IronPineOutdoors/IPC101/mechanical/enclosure/branding/reference_crosswind_concept/crosswind_detail.png

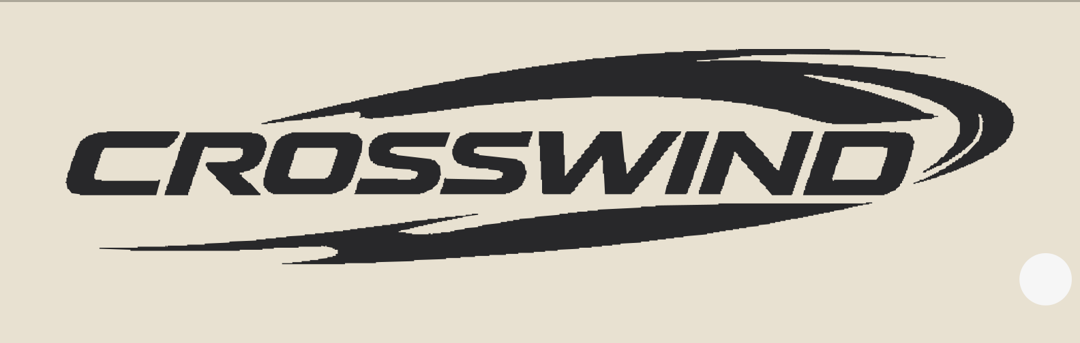
mechanical/enclosure/branding/reference_crosswind_concept/crosswind_detail.png
