IronPineOutdoors/IPC101/mechanical/enclosure/branding/reference_crosswind_concept/faceplate.png

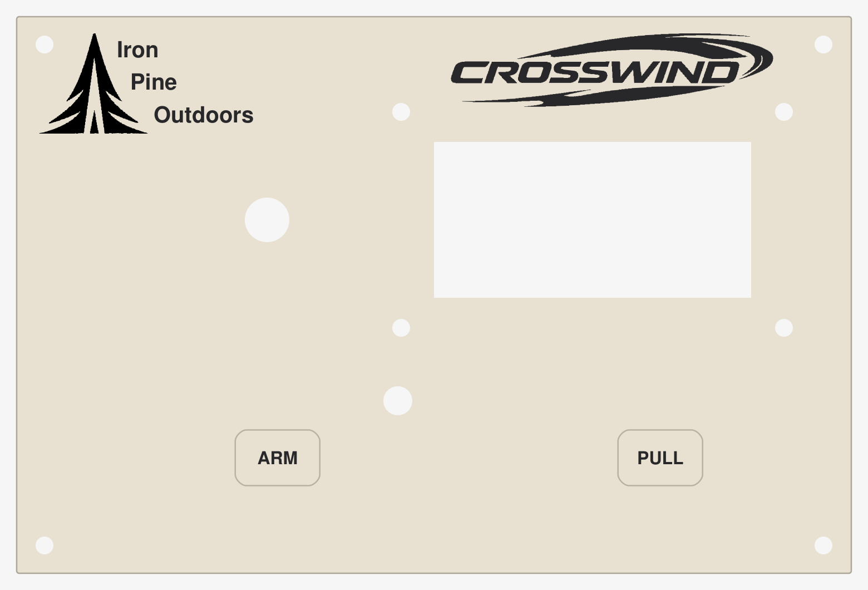
mechanical/enclosure/branding/reference_crosswind_concept/faceplate.png
