IronPineOutdoors/IPC101/mechanical/enclosure/controls/buttons/R1_button_caps_preview.png

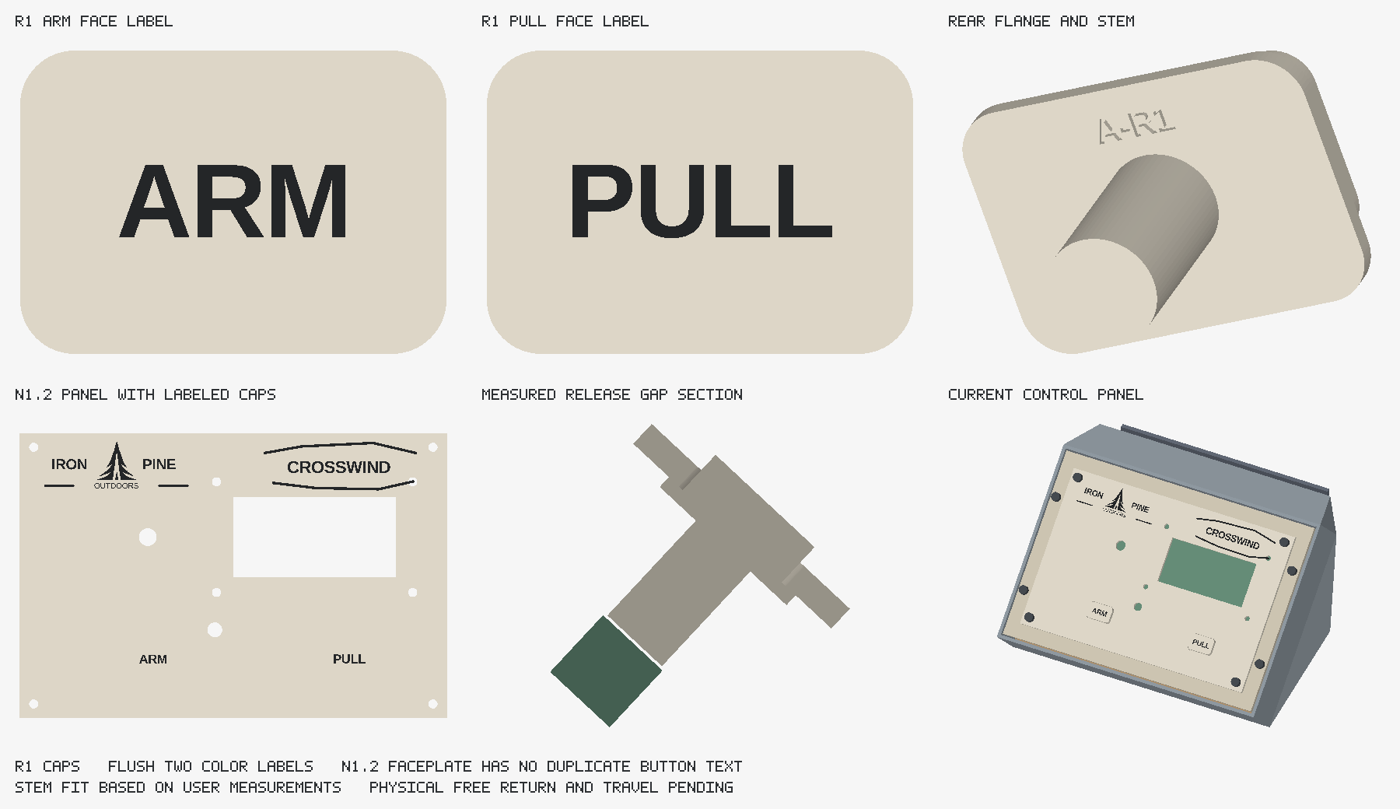
mechanical/enclosure/controls/buttons/R1_button_caps_preview.png
