IronPineOutdoors/IPC101/mechanical/enclosure/controls/led/LED_R1_preview.png

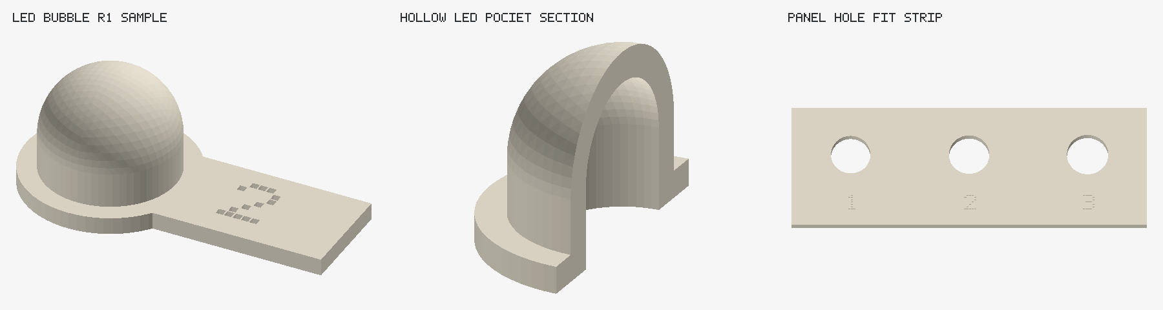
mechanical/enclosure/controls/led/LED_R1_preview.png
