IronPineOutdoors/IPC101/mechanical/enclosure/controls/stop/side-pod/STOP_S1_preview.png

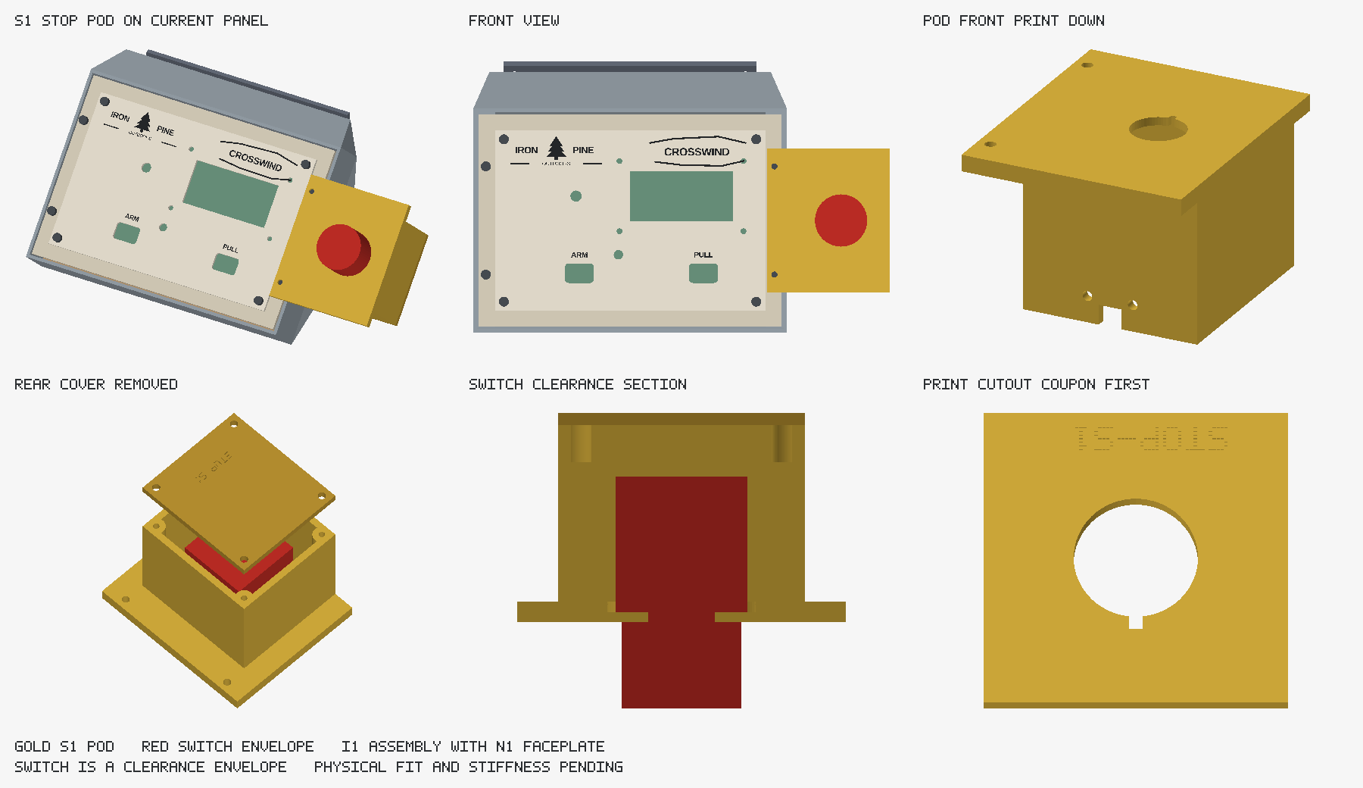
mechanical/enclosure/controls/stop/side-pod/STOP_S1_preview.png
