IronPineOutdoors/IPC101/mechanical/enclosure/controls/stop/top-mounted/TOP_STOP_R3_preview.png

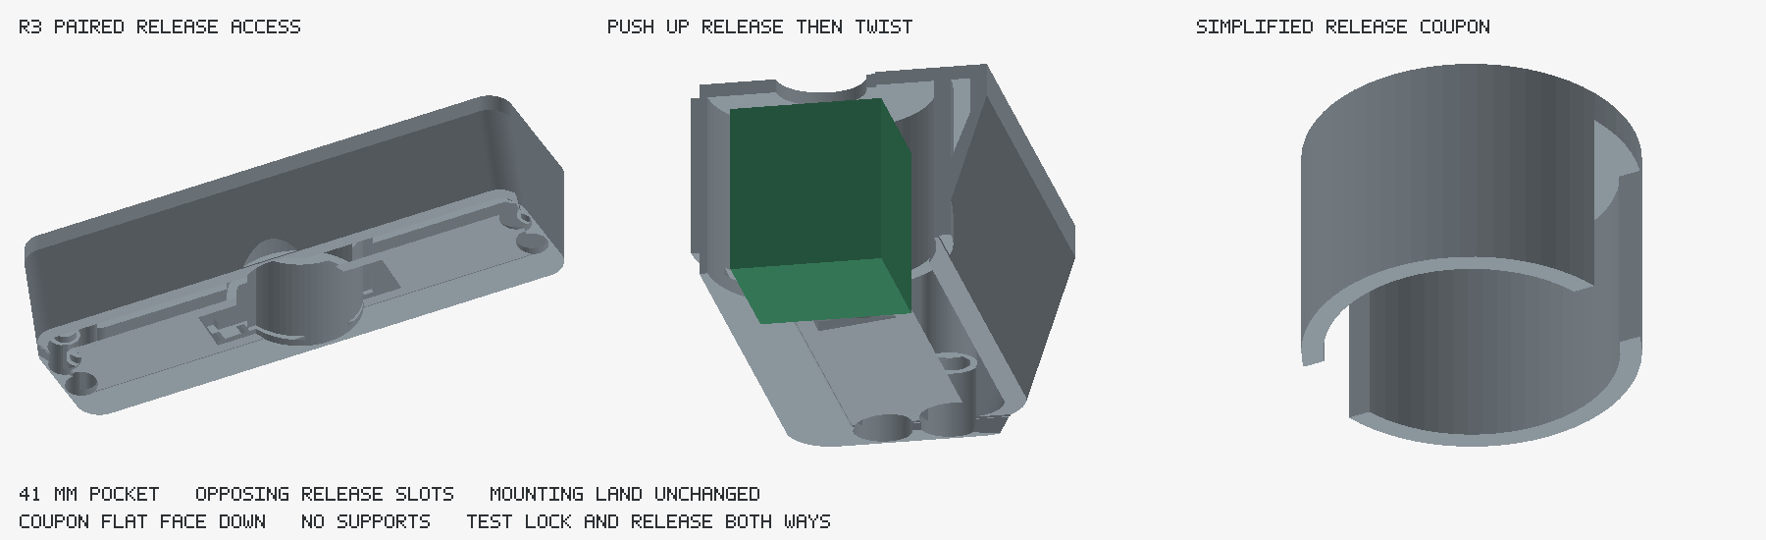
mechanical/enclosure/controls/stop/top-mounted/TOP_STOP_R3_preview.png
