IronPineOutdoors/IPC101/mechanical/enclosure/mounting/RevH_preview.png

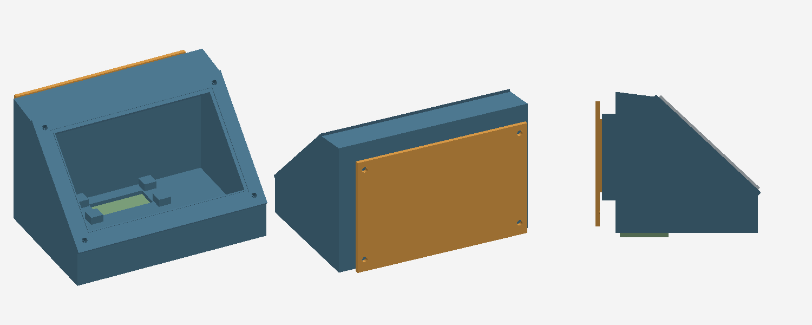
mechanical/enclosure/mounting/RevH_preview.png
