IronPineOutdoors/IPC101/mechanical/enclosure/RevI_preview.png

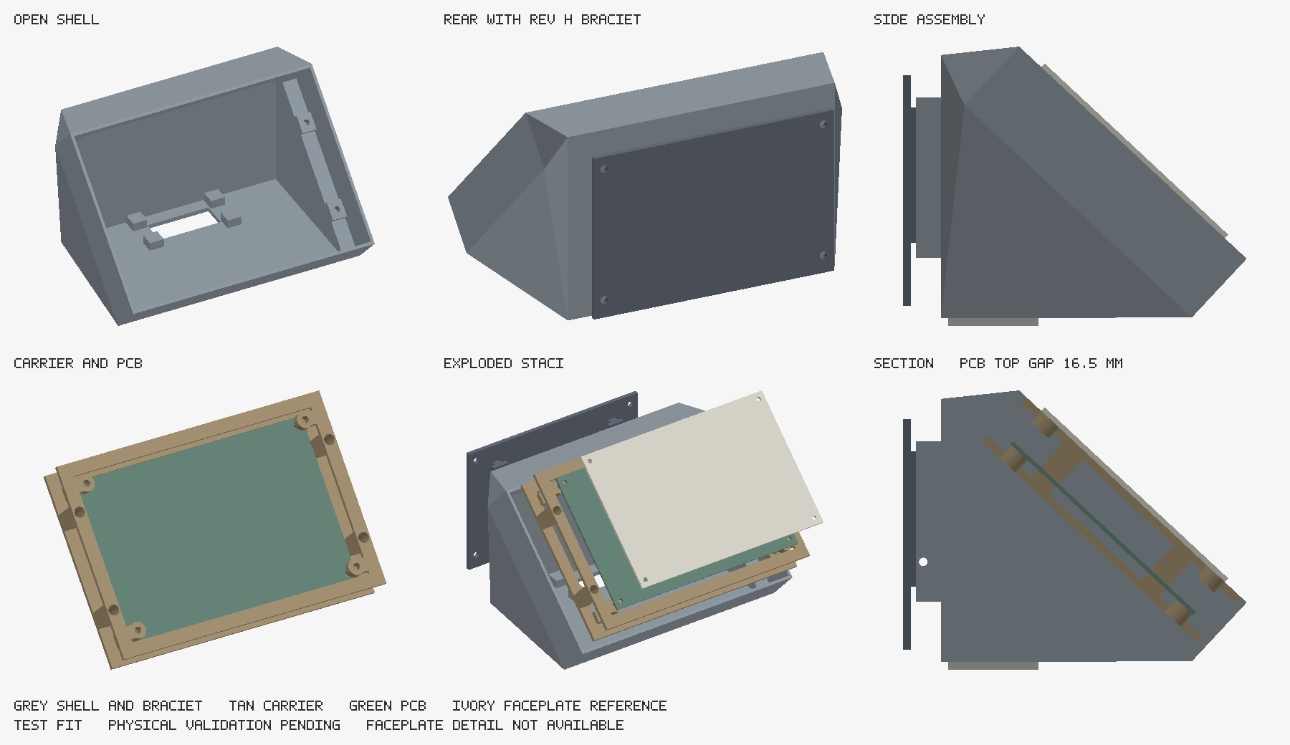
mechanical/enclosure/RevI_preview.png
