IronPineOutdoors/IPC101/mechanical/enclosure/structure/RevI1_preview.png

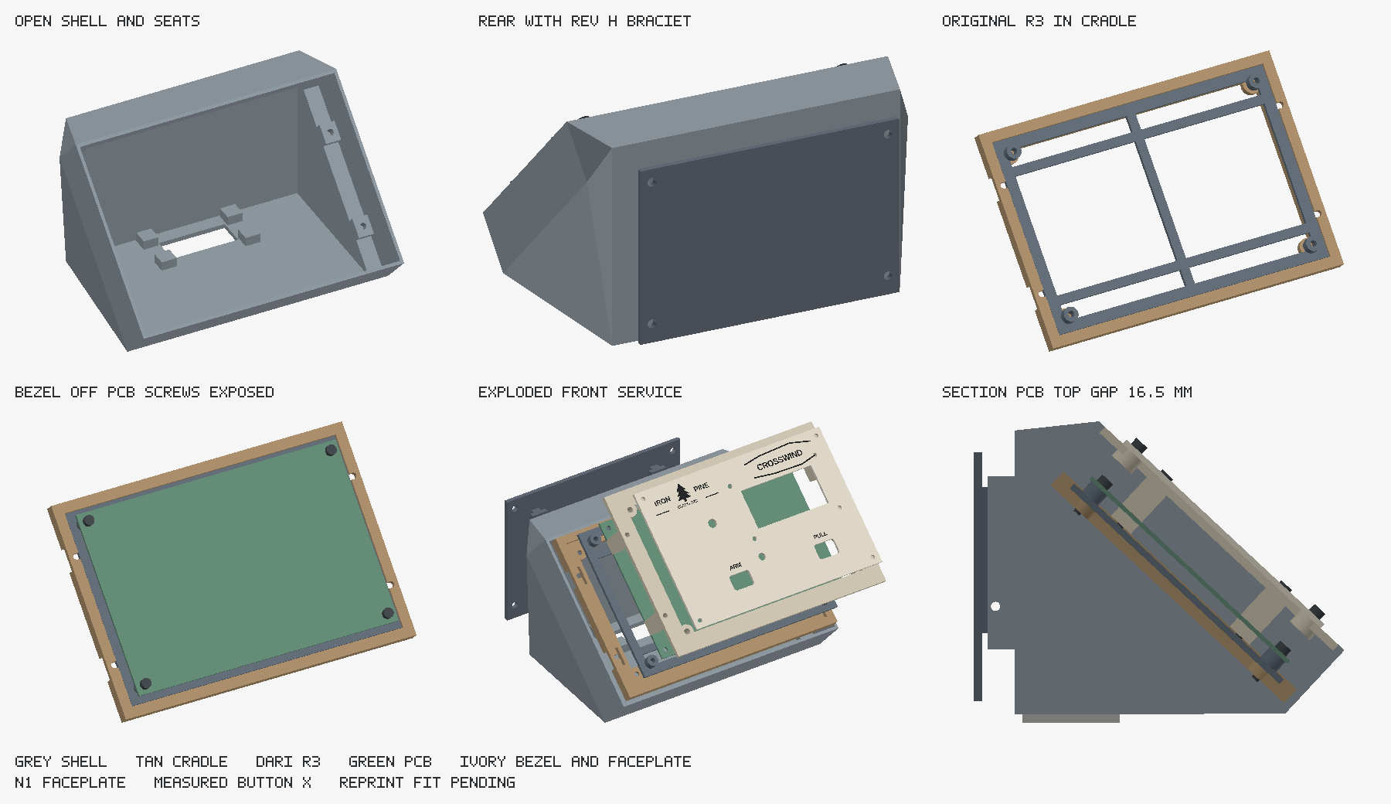
mechanical/enclosure/structure/RevI1_preview.png
