IronPineOutdoors/IPC101/mechanical/enclosure/controls/buttons/CrossWind_IPC101_PULL_Cap_R1_BLACK_AMS.stl

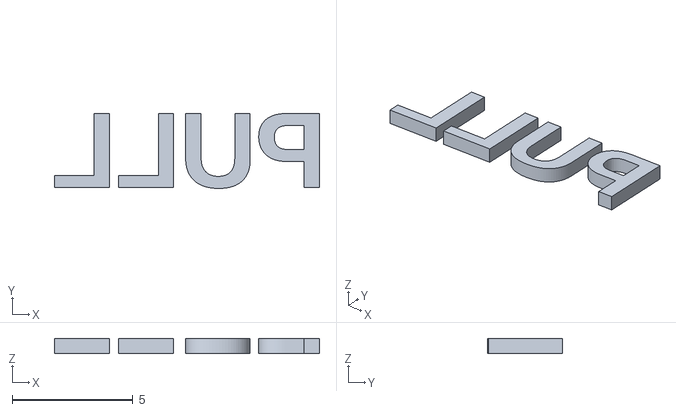
[picture p30: CAD file, 2026-09-21]
mechanical/enclosure/controls/buttons/CrossWind_IPC101_PULL_Cap_R1_BLACK_AMS.stl
11.0 x 3.10 x 0.6
