IronPineOutdoors/IPC101/mechanical/enclosure/controls/led/CrossWind_IPC101_LED_R1_Bubble_3_Bore5.7_PRINT.stl

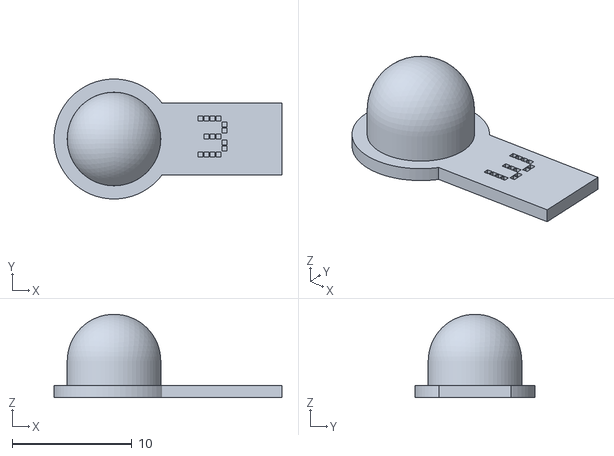
[picture p31: CAD file, 2026-09-22]
mechanical/enclosure/controls/led/CrossWind_IPC101_LED_R1_Bubble_3_Bore5.7_PRINT.stl
19.0 x 10.0 x 6.95
