IronPineOutdoors/IPC101/mechanical/enclosure/CrossWind_IPC101_Box_RevI_PRINT.stl

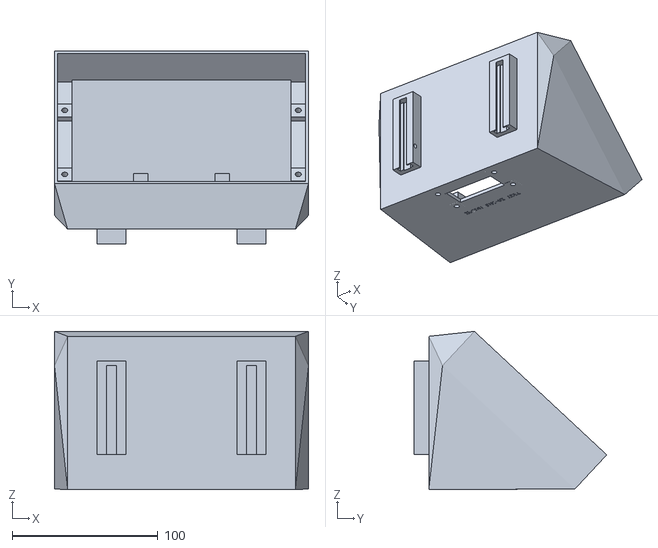
[picture p32: CAD file, 2026-09-21]
mechanical/enclosure/CrossWind_IPC101_Box_RevI_PRINT.stl
174.0 x 131.9 x 108.4
