IronPineOutdoors/IPC101/mechanical/enclosure/mounting/CrossWind_IPC101_Box_RevH_PRINT.stl

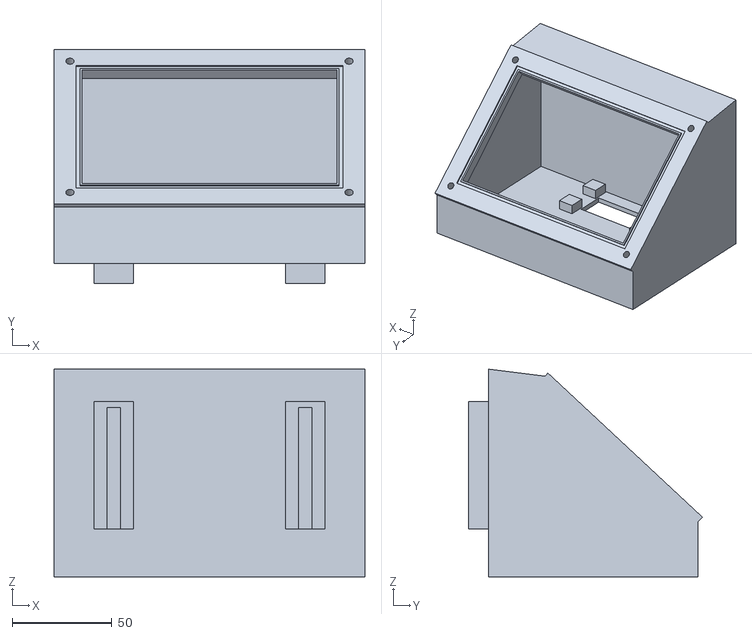
[picture p33: CAD file, 2026-09-07]
mechanical/enclosure/mounting/CrossWind_IPC101_Box_RevH_PRINT.stl
156.0 x 117.3 x 104.2
