IronPineOutdoors/IPC101/mechanical/enclosure/mounting/rear-tunnel-r1/CrossWind_IPC101_Rear_Tunnel_Base_R1_PRINT.stl

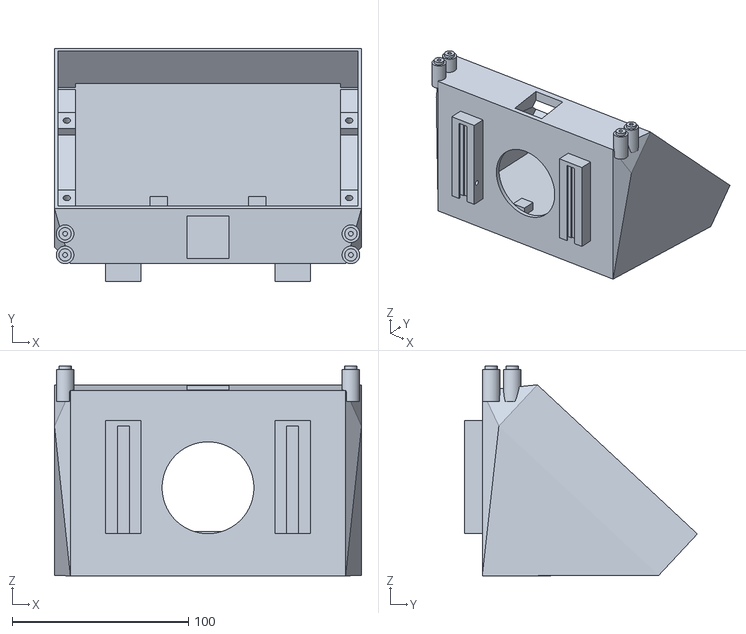
[picture p34: CAD file, 2026-09-22]
mechanical/enclosure/mounting/rear-tunnel-r1/CrossWind_IPC101_Rear_Tunnel_Base_R1_PRINT.stl
174.0 x 131.9 x 119.0
