IronPineOutdoors/IPC101/mechanical/enclosure/structure/CrossWind_IPC101_Cradle_RevI1_PRINT.stl

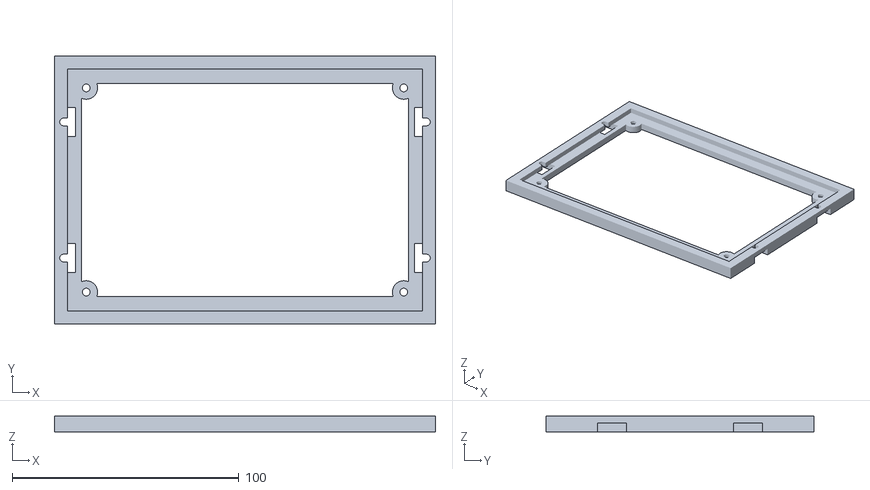
[picture p35: CAD file, 2026-09-21]
mechanical/enclosure/structure/CrossWind_IPC101_Cradle_RevI1_PRINT.stl
168.0 x 118.0 x 7.00
