IronPineOutdoors/IPC101/mechanical/panel/tpu-prototypes/P504_TPU_WEB_0.4mm.stl

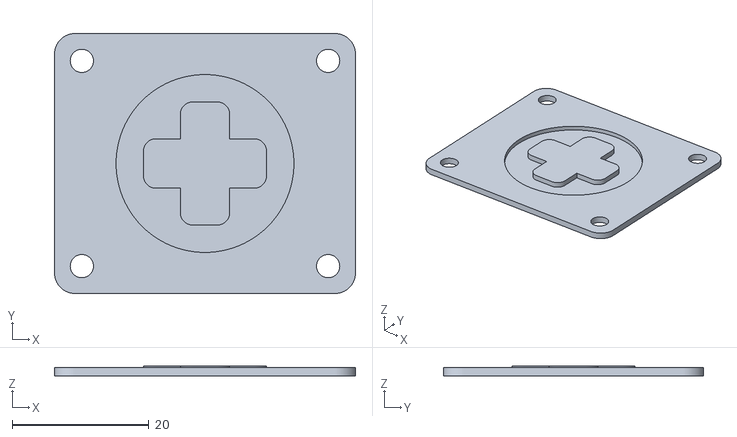
[picture p36: CAD file, 2026-09-08]
mechanical/panel/tpu-prototypes/P504_TPU_WEB_0.4mm.stl
44.0 x 38.0 x 1.40
