IronPineOutdoors/IPC101/mechanical/enclosure/controls/led/CrossWind_IPC101_LED_R1_Hole_Strip_PRINT.stl

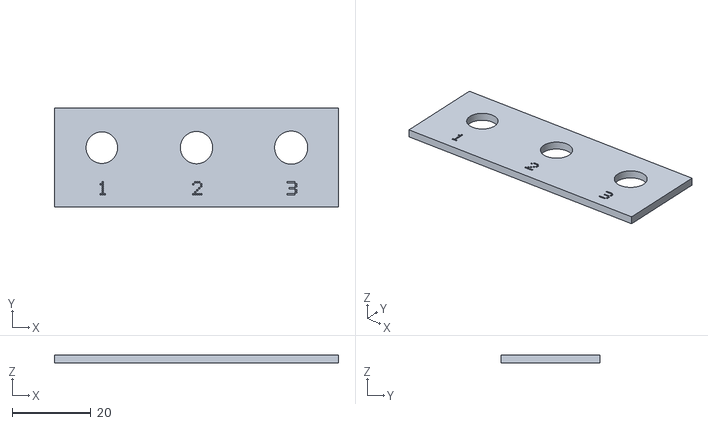
[picture p37: CAD file, 2026-09-22]
mechanical/enclosure/controls/led/CrossWind_IPC101_LED_R1_Hole_Strip_PRINT.stl
72.0 x 25.0 x 2.05
