IronPineOutdoors/IPC101/mechanical/enclosure/controls/stop/top-mounted/CrossWind_IPC101_Top_STOP_Pilot_Coupon_R1_INSTALLED.stl

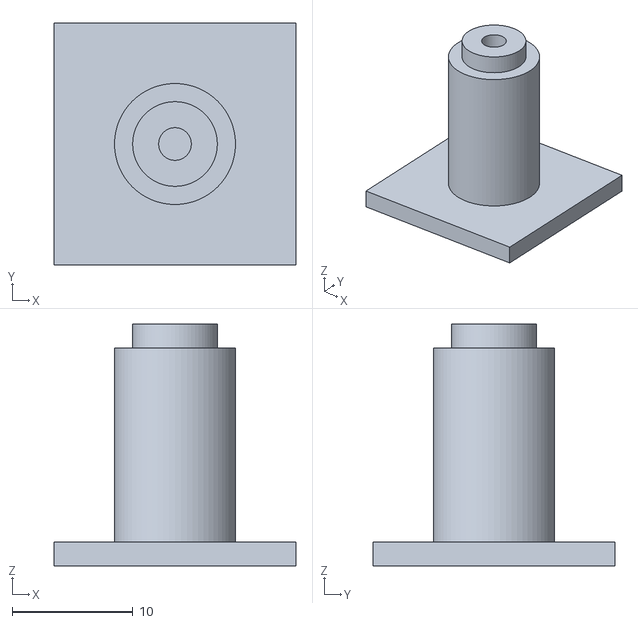
[picture p38: CAD file, 2026-09-22]
mechanical/enclosure/controls/stop/top-mounted/CrossWind_IPC101_Top_STOP_Pilot_Coupon_R1_INSTALLED.stl
20.0 x 20.0 x 20.0
