IronPineOutdoors/IPC101/mechanical/enclosure/faceplate/history/CrossWind_IPC101_Faceplate_RevN12_BLACK_AMS.stl

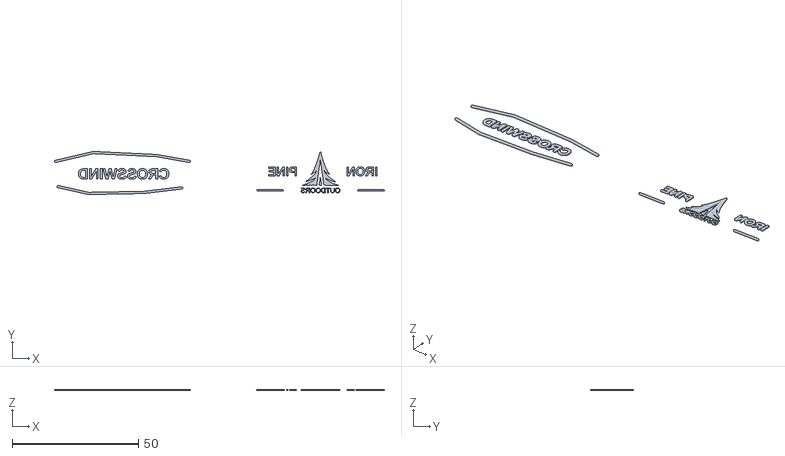
[picture p39: CAD file, 2026-09-22]
mechanical/enclosure/faceplate/history/CrossWind_IPC101_Faceplate_RevN12_BLACK_AMS.stl
130.8 x 17.1 x 0.55
