IronPineOutdoors/IPC101/mechanical/enclosure/mounting/rear-tunnel-r1/CrossWind_IPC101_Rear_Tunnel_Wall_Template_R1_PRINT.stl

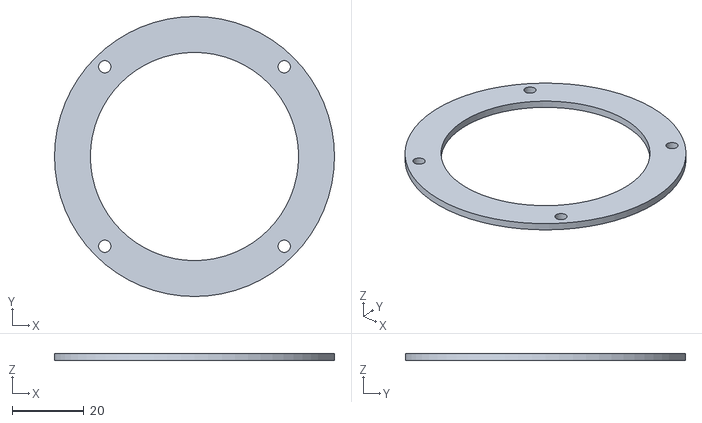
[picture p40: CAD file, 2026-09-22]
mechanical/enclosure/mounting/rear-tunnel-r1/CrossWind_IPC101_Rear_Tunnel_Wall_Template_R1_PRINT.stl
78.0 x 78.0 x 2.00
