IronPineOutdoors/IPC101/mechanical/enclosure/structure/CrossWind_IPC101_Bezel_RevI1_INSTALLED.stl

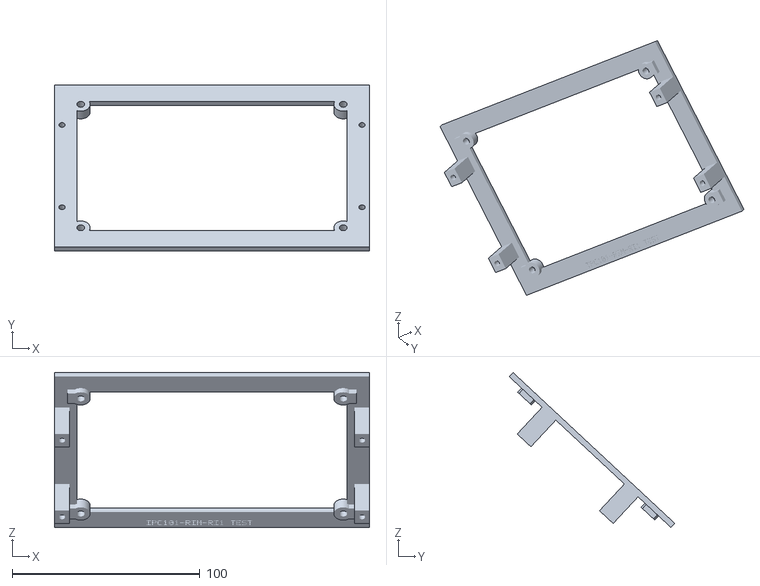
[picture p41: CAD file, 2026-09-21]
mechanical/enclosure/structure/CrossWind_IPC101_Bezel_RevI1_INSTALLED.stl
168.0 x 88.3 x 82.7
