IronPineOutdoors/IPC101/mechanical/panel/tpu-prototypes/P504_CLAMP_FRAME_RIGID.stl

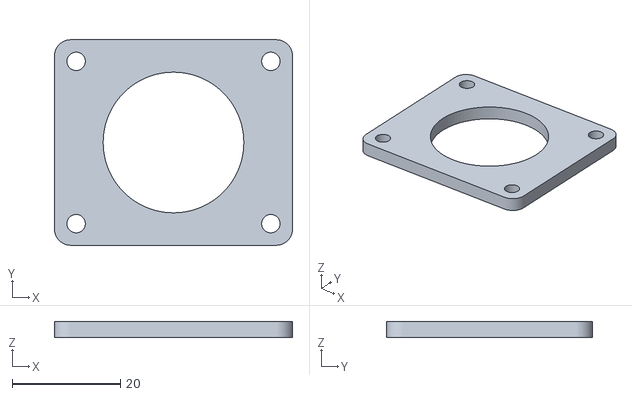
[picture p42: CAD file, 2026-09-08]
mechanical/panel/tpu-prototypes/P504_CLAMP_FRAME_RIGID.stl
44.0 x 38.0 x 3.00
