IronPineOutdoors/IPC101/mechanical/enclosure/controls/buttons/CrossWind_IPC101_ARM_Cap_R1_BLACK_AMS.stl

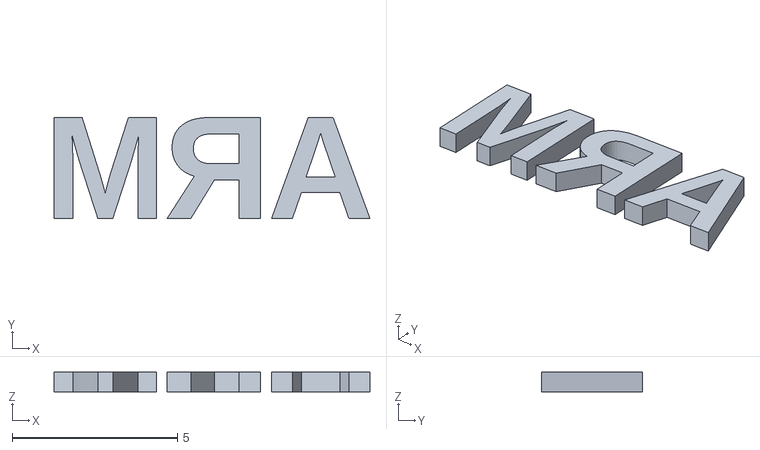
[picture p43: CAD file, 2026-09-21]
mechanical/enclosure/controls/buttons/CrossWind_IPC101_ARM_Cap_R1_BLACK_AMS.stl
9.56 x 3.06 x 0.6
