IronPineOutdoors/IPC101/mechanical/enclosure/CrossWind_IPC101_Carrier_RevI_PRINT.stl

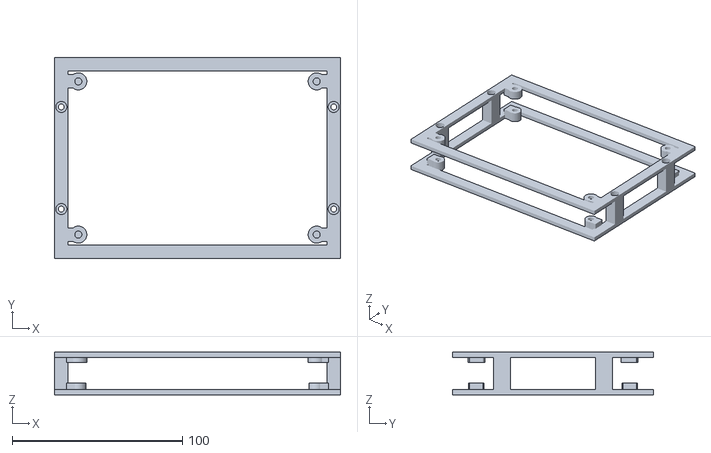
[picture p44: CAD file, 2026-09-21]
mechanical/enclosure/CrossWind_IPC101_Carrier_RevI_PRINT.stl
168.0 x 118.0 x 25.1
