IronPineOutdoors/IPC101/mechanical/enclosure/mounting/CrossWind_IPC101_Wiring_Plate_RevH_INSTALLED.stl

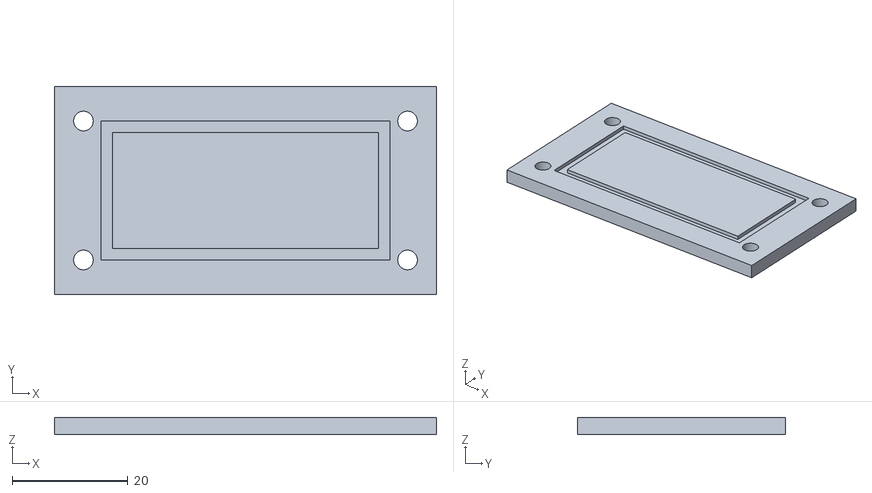
[picture p45: CAD file, 2026-09-07]
mechanical/enclosure/mounting/CrossWind_IPC101_Wiring_Plate_RevH_INSTALLED.stl
66.0 x 36.0 x 3.00
