IronPineOutdoors/IPC101/mechanical/enclosure/mounting/rear-tunnel-r1/CrossWind_IPC101_Rear_Tunnel_Bracket_R1_INSTALLED.stl

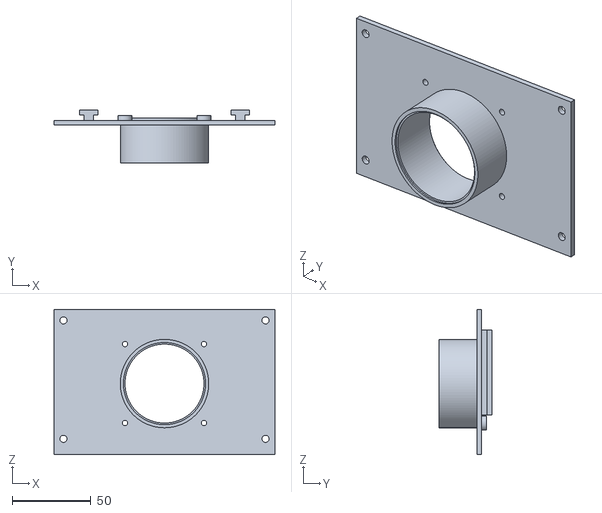
[picture p46: CAD file, 2026-09-22]
mechanical/enclosure/mounting/rear-tunnel-r1/CrossWind_IPC101_Rear_Tunnel_Bracket_R1_INSTALLED.stl
140.0 x 33.7 x 92.0
