IronPineOutdoors/IPC101/mechanical/enclosure/CrossWind_IPC101_Carrier_RevI_INSTALLED.stl

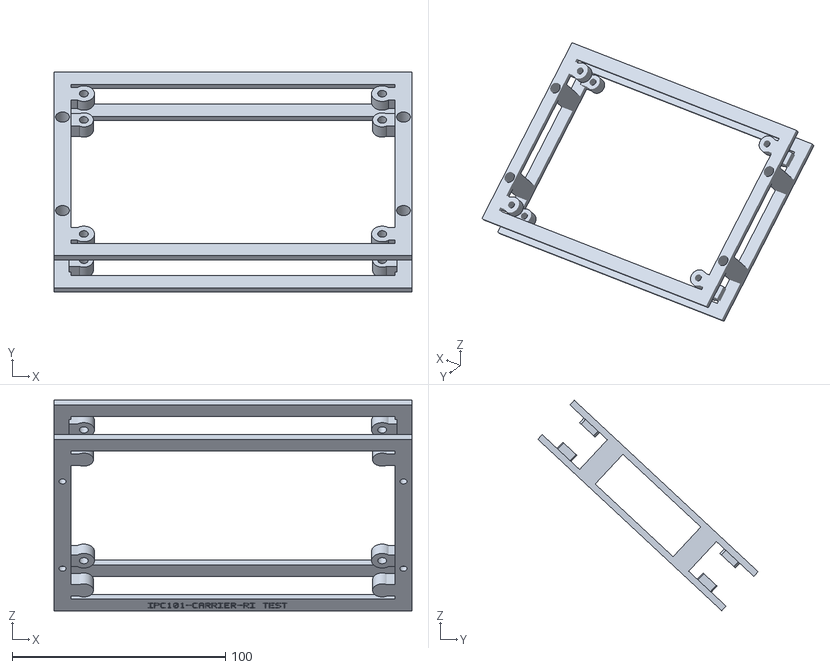
[picture p47: CAD file, 2026-09-21]
mechanical/enclosure/CrossWind_IPC101_Carrier_RevI_INSTALLED.stl
168.0 x 103.4 x 98.8
