IronPineOutdoors/IPC101/mechanical/enclosure/structure/CrossWind_IPC101_Bezel_RevI1_PRINT.stl

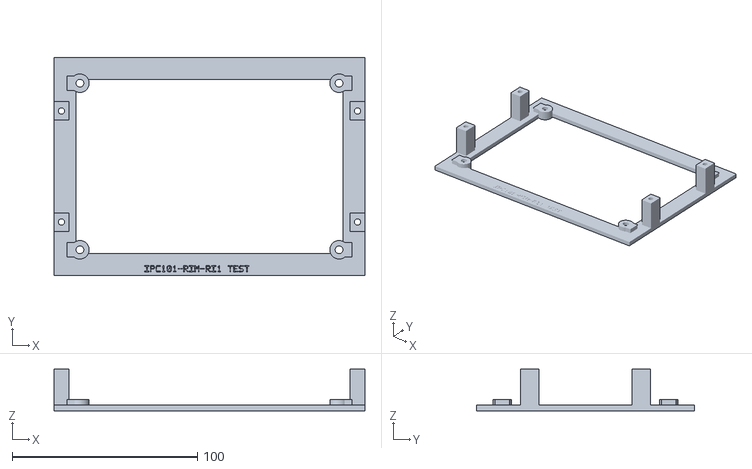
[picture p48: CAD file, 2026-09-21]
mechanical/enclosure/structure/CrossWind_IPC101_Bezel_RevI1_PRINT.stl
168.0 x 118.0 x 22.5
