IronPineOutdoors/IPC101/mechanical/panel/tpu-prototypes/ARM_PULL_CLAMP_FRAME_RIGID.stl

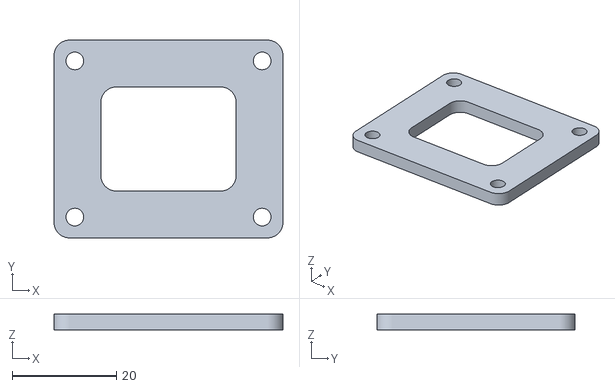
[picture p49: CAD file, 2026-09-08]
mechanical/panel/tpu-prototypes/ARM_PULL_CLAMP_FRAME_RIGID.stl
44.0 x 38.0 x 3.00
