IronPineOutdoors/IPC101/mechanical/enclosure/CrossWind_IPC101_Control_Box_RevG_PRINT.stl

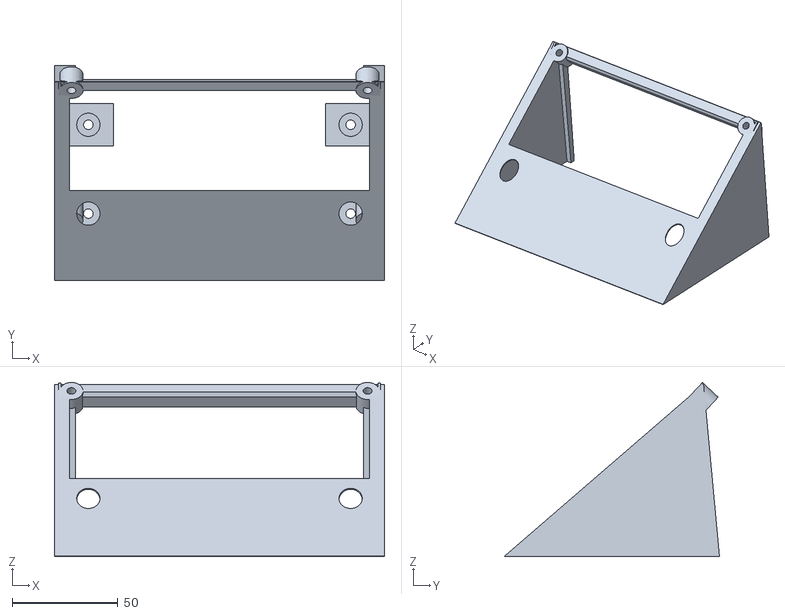
[picture p50: CAD file, 2026-09-05]
mechanical/enclosure/CrossWind_IPC101_Control_Box_RevG_PRINT.stl
156.0 x 101.6 x 82.3
