IronPineOutdoors/IPC101/mechanical/panel/tpu-prototypes/P504_TPU_WEB_0.8mm.stl

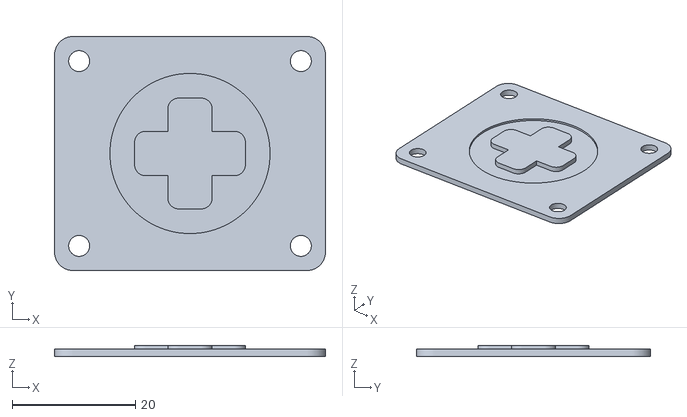
[picture p51: CAD file, 2026-09-08]
mechanical/panel/tpu-prototypes/P504_TPU_WEB_0.8mm.stl
44.0 x 38.0 x 1.80
