IronPineOutdoors/IPC101/mechanical/enclosure/faceplate/history/CrossWind_IPC101_Faceplate_RevN1_BLACK_AMS.stl

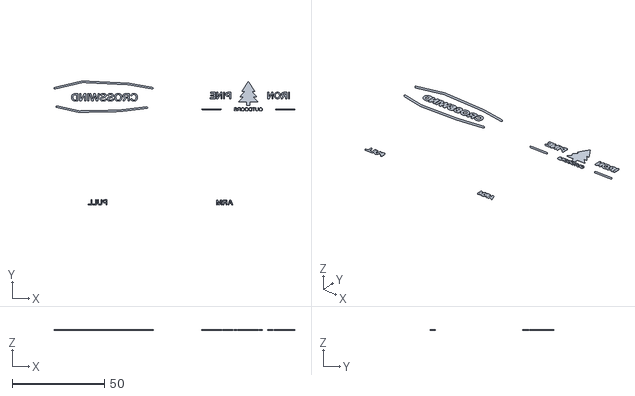
[picture p52: CAD file, 2026-09-21]
mechanical/enclosure/faceplate/history/CrossWind_IPC101_Faceplate_RevN1_BLACK_AMS.stl
130.8 x 67.4 x 0.55
