IronPineOutdoors/IPC101/hardware/fabrication/IPC101_RevC/IPC101_RevC_MaskFix_bottom.png

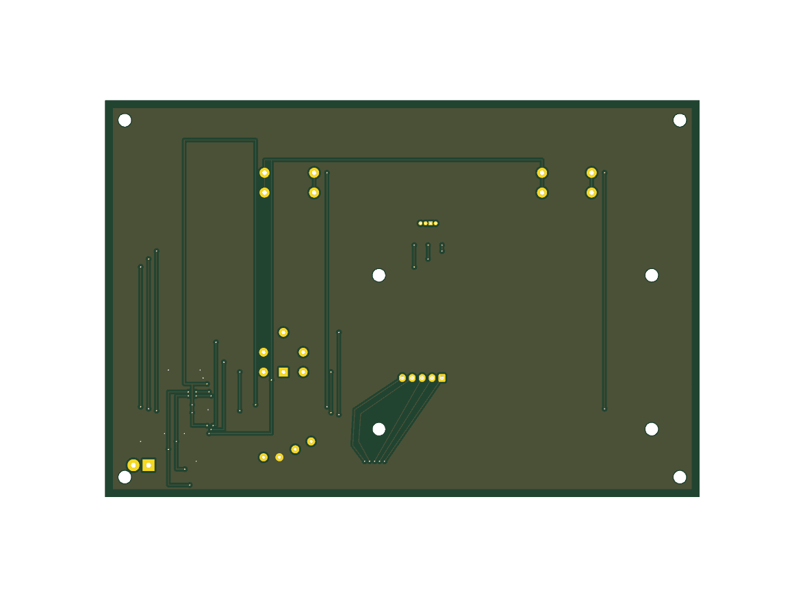
hardware/fabrication/IPC101_RevC/IPC101_RevC_MaskFix_bottom.png
