IronPineOutdoors/IPC101/mechanical/enclosure/faceplate/history/N1_faceplate_preview.png

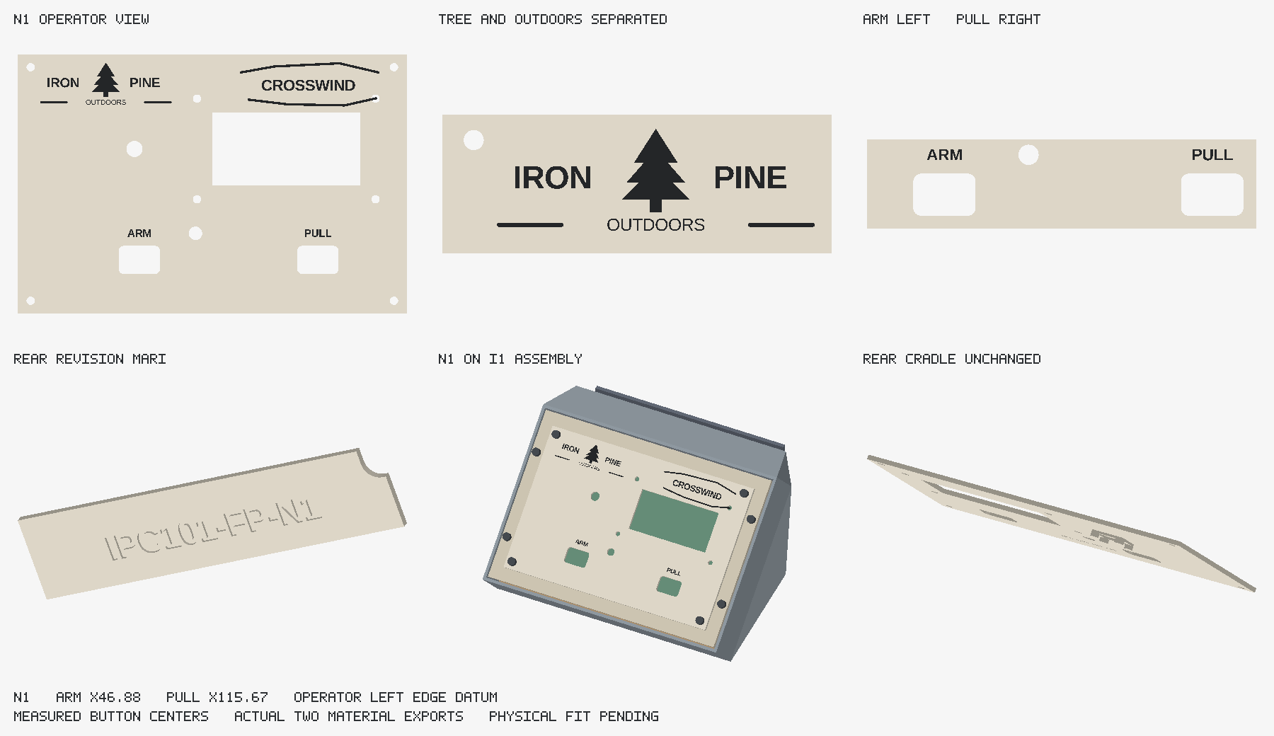
mechanical/enclosure/faceplate/history/N1_faceplate_preview.png
