IronPineOutdoors/IPC101/mechanical/enclosure/faceplate/history/N13_faceplate_preview.png

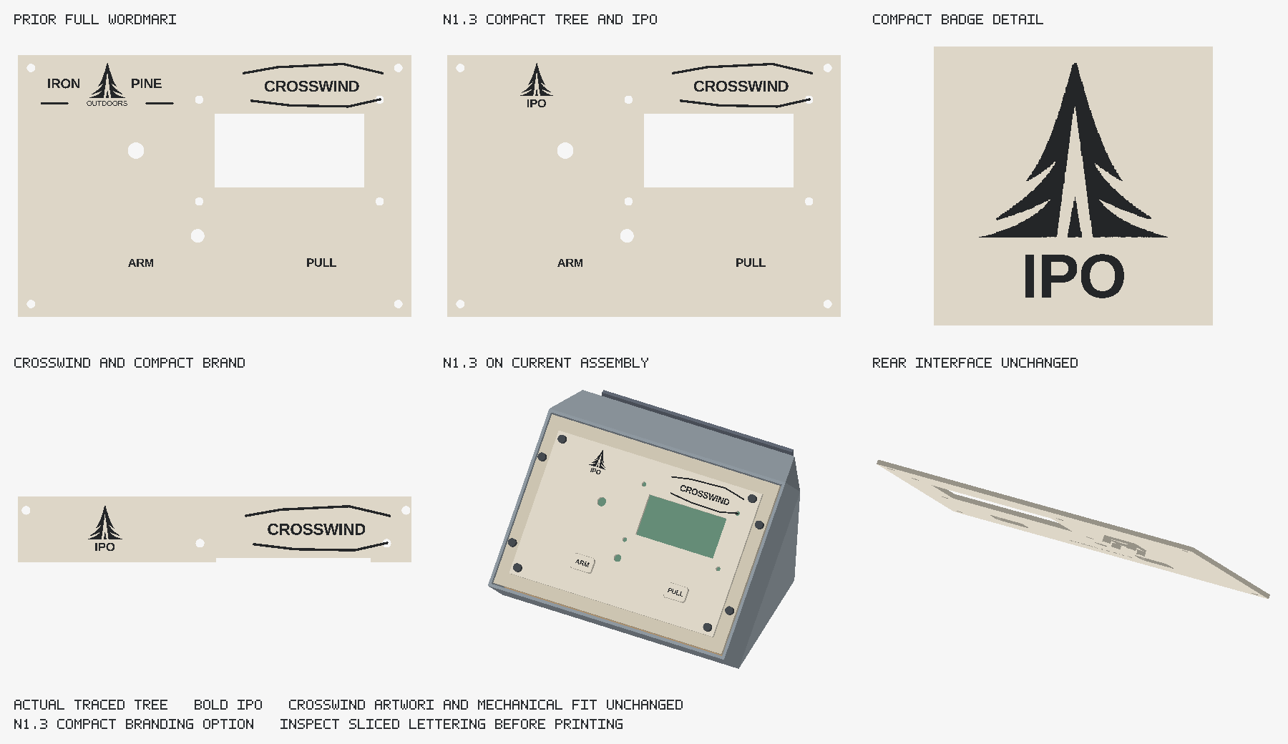
mechanical/enclosure/faceplate/history/N13_faceplate_preview.png
